Spirou42/metaPixel/Resources/Fire.jpg

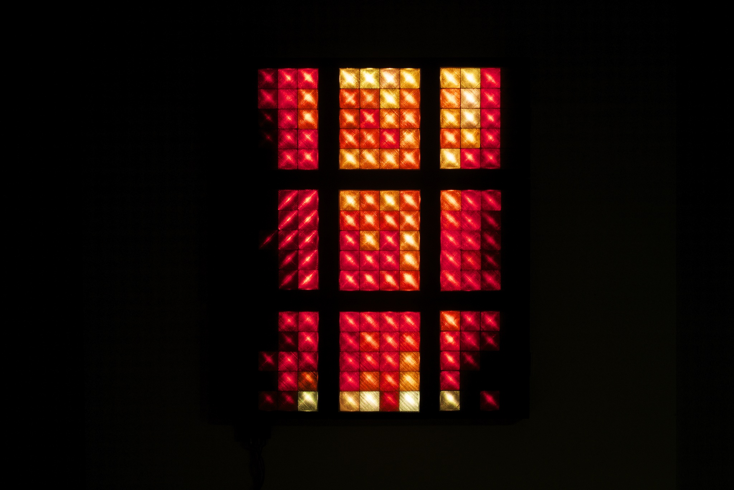
Resources/Fire.jpg
