Spirou42/metaPixel/Resources/inside.jpg

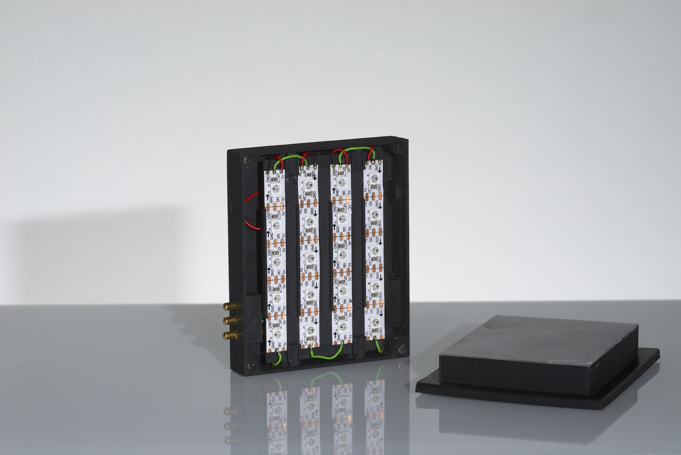
Resources/inside.jpg
