Spirou42/metaPixel/Resources/inside_2.jpg

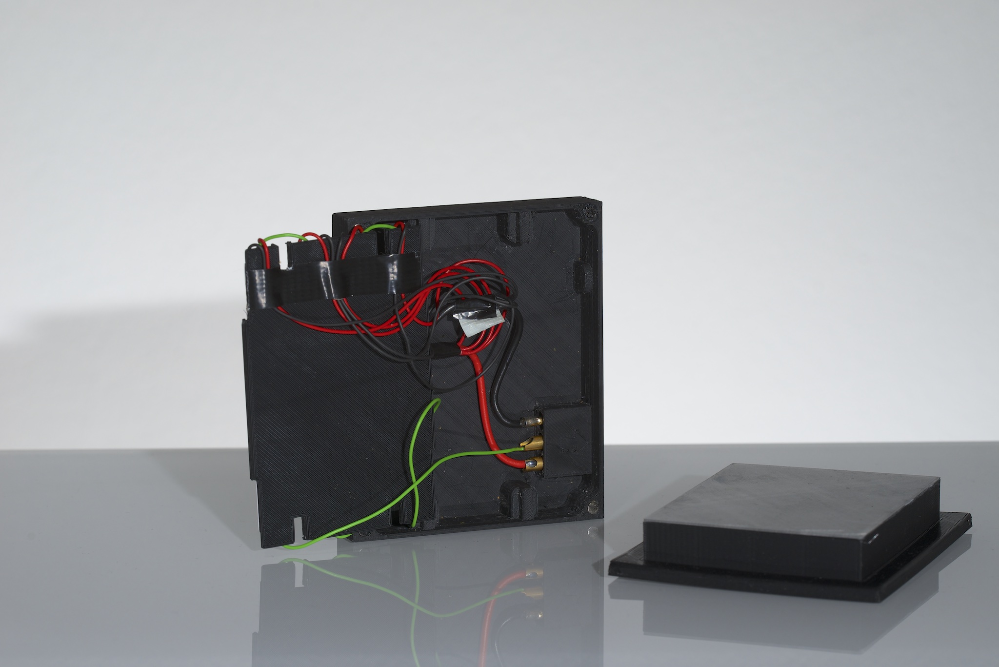
Resources/inside_2.jpg
