Spirou42/metaPixel/Resources/lightshow.jpg

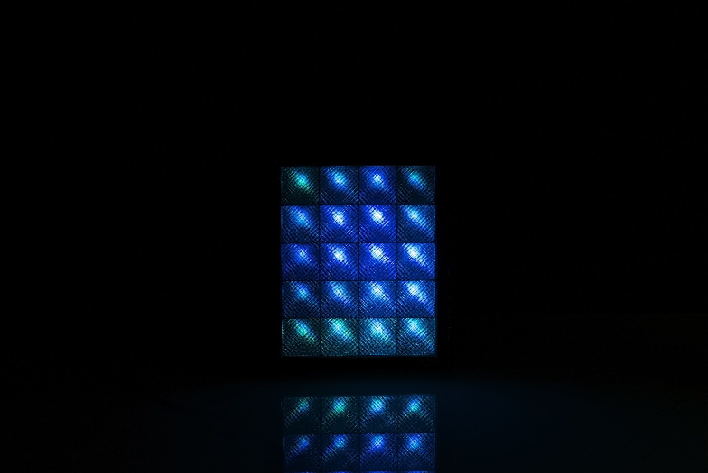
Resources/lightshow.jpg
