Spirou42/metaPixel/Resources/metaPixel-FullColoured.png

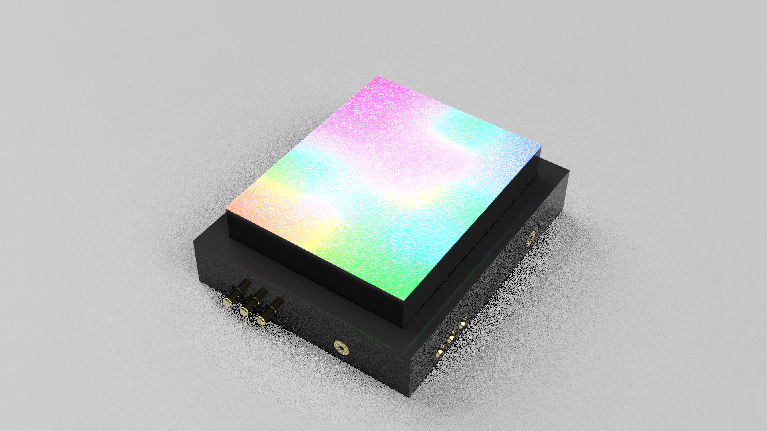
Resources/metaPixel-FullColoured.png
