Spirou42/metaPixel/Resources/metaPixel.jpg

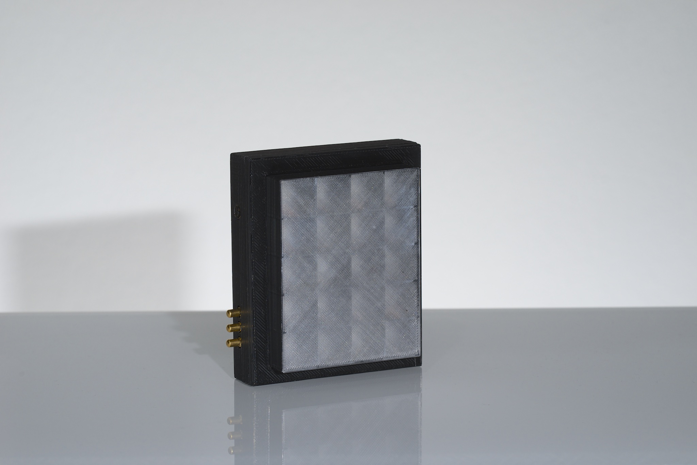
Resources/metaPixel.jpg
