Spirou42/metaPixel/Resources/STCRIMP1.png

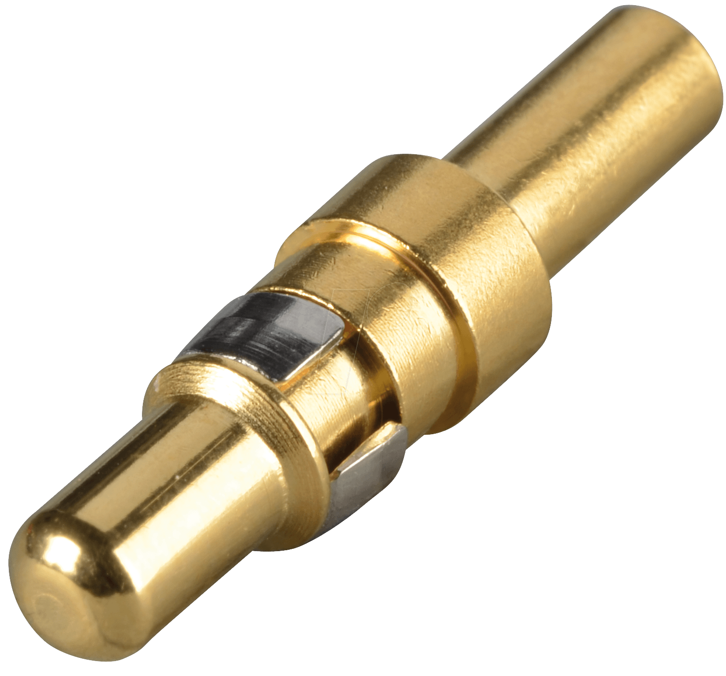
Resources/STCRIMP1.png
