Spirou42/metaPixel/Resources/Components.jpg

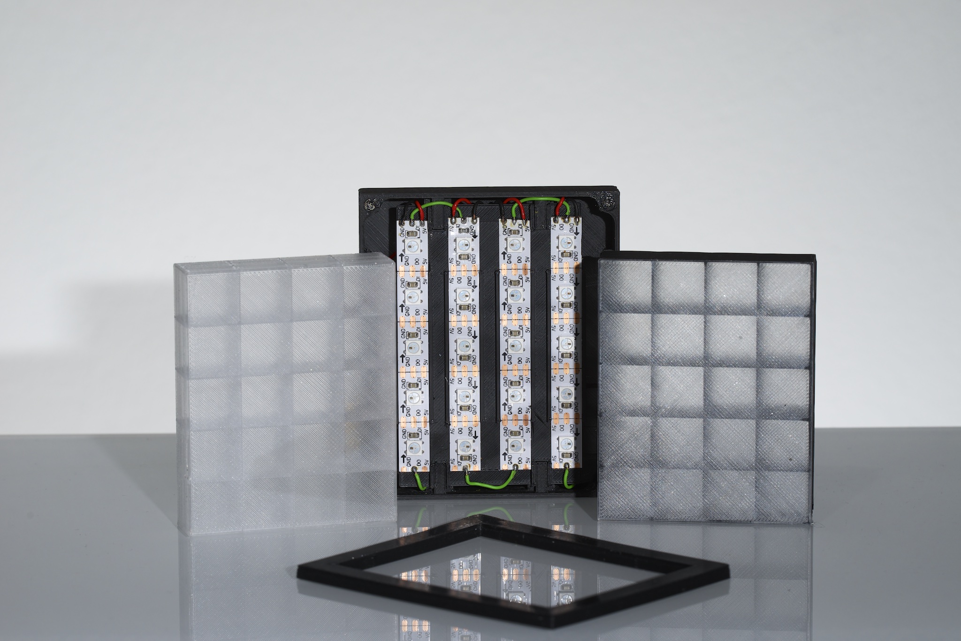
Resources/Components.jpg
