Spirou42/metaPixel/Software/metaPixel/Effect.hpp

/**
	 Effect.h
	 @description: simple wrapper class for effect programs

**/

#ifndef __EFFECT_H__
#define __EFFECT_H__
#include <Arduino.h>
#include <Streaming.h>
#include "VT100Stream.hpp"
#include "Parameter.hpp"


class Effect
{
public:

	const char *name;																		///< the name of the effect
	Effect():name(""){};
	Effect(const char *p):name(p){};
	/**
		called after the effect programm got switch and before the first frame.
		put your book keeping and initialization in here
	*/
	virtual void startEffect(){}; 											///< book keeping on startup

	/**
		called for each and every fram
	*/
	virtual void frame(unsigned long now){};

	/**
	called after the last frame. restore your book keeping here and clean up your dynamic objects
	*/
	virtual void stopEffect(){};


	virtual void printParameter(Print& stream){};
	const char * getName(){return name;}
	/**
	* Parameter handling
	*/
	virtual size_t 					numberOfParameters(){return 0;};
	virtual Parameter16_t* 	parameterAt(size_t idx){Serial <<"Gnartz";return NULL;};
	virtual const char* 		parameterNameAt(size_t idx){Serial <<"Gnartz2";return NULL;};

	/**
	* Parameter16_t helper
	*/
	int16_t getValueFor(Parameter16_t *someValue,int16_t defaultValue=0){
			if(NULL!=someValue){
				return someValue->value->currentValue();
			}else{
				return defaultValue;
			}
	};

	void setValueFor(Parameter16_t *someValue, int16_t value){
		if(NULL != someValue){
			someValue->value->SetValue(value);
		}
	};
	void initValueFor(Parameter16_t * someValue, int16_t value){
		if(NULL != someValue){
			someValue->value->initTo(value);
		}
	};
	void setMaxValueFor(Parameter16_t *someValue,int16_t maxVal ){
			if(NULL!=someValue){
				someValue->maxValue = maxVal;
			}
	};
	const char getCodeFor(Parameter16_t *someValue)
	{
		if(NULL!=someValue){return someValue->code;}else{return 0x00;}
	};
	friend Print& operator<<(Print &output, Effect *d){
		output<<"Effect: "<<bold<<d->name<<normal<<endl;
		output<<"Parameters: ";
		d->printParameter(output);
		return output;
	}

	String* parameterString(){
		String* parameterString= new String(" ");
		for(size_t i=0;i<this->numberOfParameters();i++){
			Parameter16_t * param= parameterAt(i);
			*parameterString += 	*param->getCommandString();
		}
		*parameterString += " ";
		*parameterString += *parameterArray[1].getCommandString();
		*parameterString += *parameterArray[2].getCommandString();
		*parameterString += *parameterArray[4].getCommandString();
		*parameterString += *parameterArray[5].getCommandString();
		return parameterString;
	}
};

//typedef int (*queuedFunction)(unsigned long,void* userData);
int effectRunner(unsigned long now, void* userdata);

#endif
